grafmar/LyncDisplayLight/src/LyncDisplayLight/FreeSans12pt8b.h

const uint8_t FreeSans12pt8bBitmaps[] PROGMEM = {
  0xFF, 0xFF, 0xFF, 0xF0, 0xF0, 0xCF, 0x3C, 0xF3, 0x8A, 0x20, 0x06, 0x30,
  0x31, 0x03, 0x18, 0x18, 0xC7, 0xFF, 0xBF, 0xFC, 0x31, 0x03, 0x18, 0x18,
  0xC7, 0xFF, 0xBF, 0xFC, 0x31, 0x01, 0x18, 0x18, 0xC0, 0xC6, 0x06, 0x30,
  0x04, 0x03, 0xE1, 0xFF, 0x72, 0x6C, 0x47, 0x88, 0xF1, 0x07, 0x20, 0x7E,
  0x03, 0xF0, 0x17, 0x02, 0x3C, 0x47, 0x88, 0xF1, 0x1B, 0x26, 0x7F, 0xC3,
  0xE0, 0x10, 0x02, 0x00, 0x00, 0x06, 0x03, 0xC0, 0x40, 0x7E, 0x0C, 0x0E,
  0x70, 0x80, 0xC3, 0x18, 0x0C, 0x31, 0x00, 0xE7, 0x30, 0x07, 0xE6, 0x00,
  0x3C, 0x40, 0x00, 0x0C, 0x7C, 0x00, 0x8F, 0xE0, 0x19, 0xC7, 0x01, 0x18,
  0x30, 0x31, 0x83, 0x02, 0x1C, 0x70, 0x40, 0xFE, 0x04, 0x07, 0xC0, 0x0F,
  0x00, 0x7E, 0x03, 0x9C, 0x0C, 0x30, 0x30, 0xC0, 0xE7, 0x01, 0xF8, 0x03,
  0x80, 0x3E, 0x01, 0xCC, 0x6E, 0x19, 0xB0, 0x7C, 0xC0, 0xF3, 0x03, 0xCE,
  0x1F, 0x9F, 0xE6, 0x1E, 0x1C, 0xFF, 0xA0, 0x08, 0x8C, 0x66, 0x31, 0x98,
  0xC6, 0x31, 0x8C, 0x63, 0x08, 0x63, 0x08, 0x61, 0x0C, 0x20, 0x82, 0x18,
  0xC3, 0x18, 0xC3, 0x18, 0xC6, 0x31, 0x8C, 0x62, 0x31, 0x88, 0xC4, 0x62,
  0x00, 0x10, 0x23, 0x5B, 0xE3, 0x8D, 0x91, 0x00, 0x0C, 0x03, 0x00, 0xC0,
  0x30, 0xFF, 0xFF, 0xF0, 0xC0, 0x30, 0x0C, 0x03, 0x00, 0xC0, 0xF5, 0x60,
  0xFF, 0xF0, 0xF0, 0x02, 0x0C, 0x10, 0x20, 0xC1, 0x02, 0x0C, 0x10, 0x20,
  0xC1, 0x02, 0x0C, 0x10, 0x20, 0xC1, 0x00, 0x1F, 0x07, 0xF1, 0xC7, 0x30,
  0x6E, 0x0F, 0x80, 0xF0, 0x1E, 0x03, 0xC0, 0x78, 0x0F, 0x01, 0xE0, 0x3C,
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
  {   731,  11,  18,  14,    2,  -17 },   // 0x46 'F'
  {   756,  16,  18,  18,    1,  -17 },   // 0x47 'G'
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

const GFXfont FreeSans12pt8b PROGMEM = {
  (uint8_t  *)FreeSans12pt8bBitmaps,
  (GFXglyph *)FreeSans12pt8bGlyphs,
  0x20, 0xFF, 28 };

// Approx. 7597 bytes
